monome/mk/firmware/default/button.h

/* 
 *  Copyright (C) 2006, Joe Lake, monome.org
 * 
 *  This file is part of 40h.
 *
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
 *  $Id: button.h,v. 1.1.1.1 2006/05/02 1:01:22
 */

#ifndef __BUTTON_H__
#define __BUTTON_H__

#include <inttypes.h>

#define kButtonEventQueueSize 32

#define kButtonStateDown 1
#define kButtonStateUp   0

#define kButtonDownEvent 1
#define kButtonUpEvent   0

#define kButtonDownDefaultDebounceCount 0
#define kButtonUpDefaultDebounceCount   24

#define kButtonNewEvent   1
#define kButtonNoEvent    0

extern uint8_t button_current[32],             // bitmap of physical button state (depressed or released)
             button_last[32],                // bitmap of physical button state last time buttons were read
			button_state[32],              // bitmap of debounced button state
   			button_debounce_count[32][8],   // debounce counters for each button
             button_event[32];               // queued button events (kButtonDownEvent or kButtonDownEvent)

void buttonInit(void);
void buttonCheck(uint8_t row, uint8_t index);


#endif
